Y-modify/YamaX-3.0/Designs/AXBoard/AX-03r/Models/pcb.png

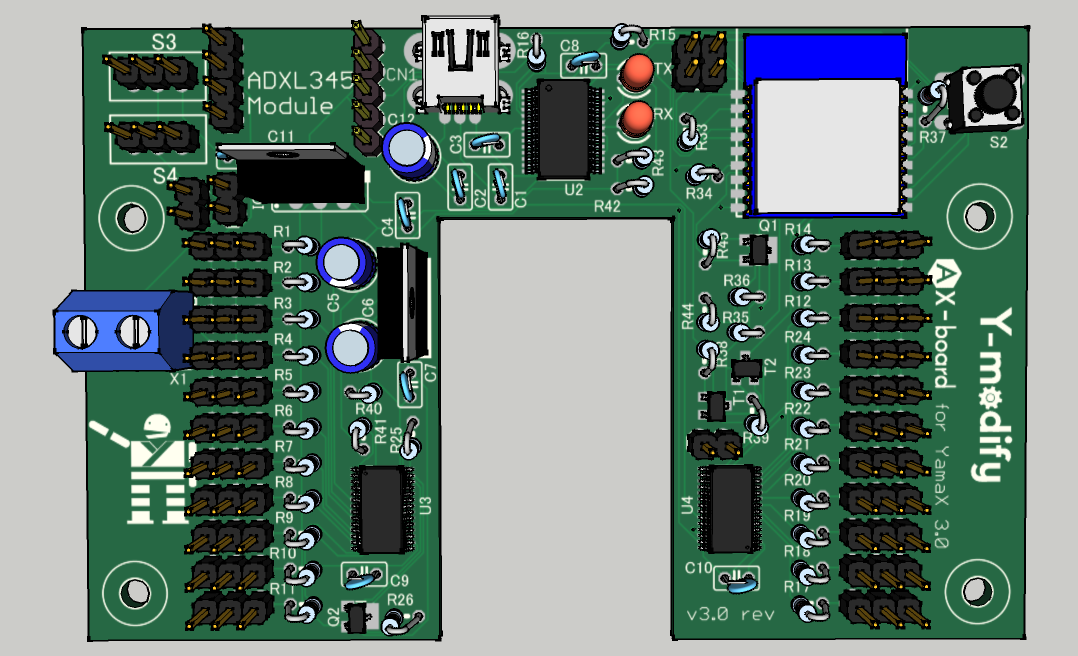
Designs/AXBoard/AX-03r/Models/pcb.png
