Y-modify/YamaX-3.0/Designs/AXBoard/AX-03r/Models/pcb/eagleUp_AX-03r_top_board.png

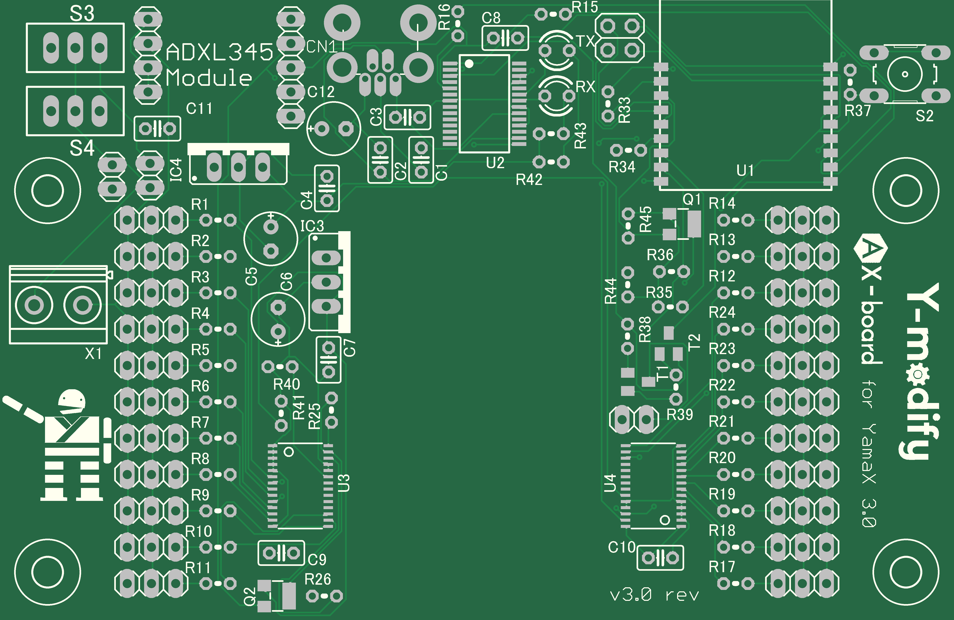
Designs/AXBoard/AX-03r/Models/pcb/eagleUp_AX-03r_top_board.png
