Y-modify/YamaX-3.0/Designs/AXBoard/AX-03r/Previews/Board.png

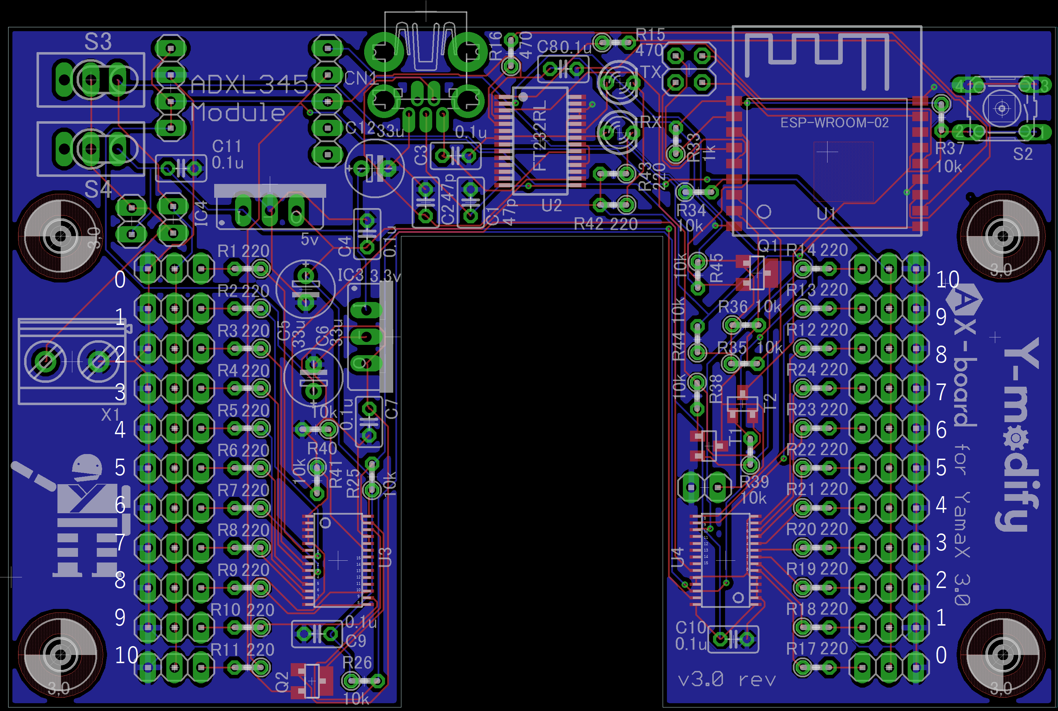
Designs/AXBoard/AX-03r/Previews/Board.png
