Y-modify/YamaX-3.0/Designs/AXBoard/AX-03r/Previews/Front.png

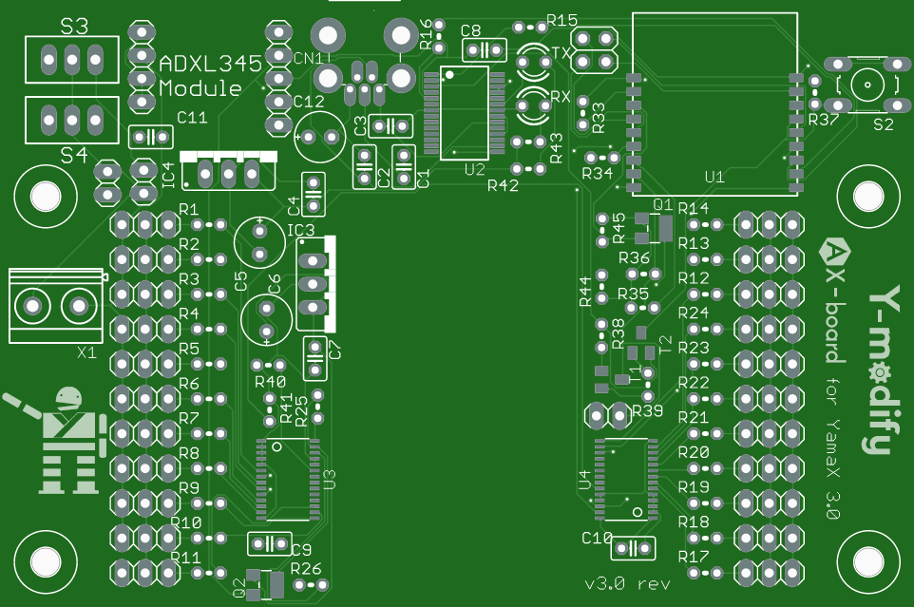
Designs/AXBoard/AX-03r/Previews/Front.png
