Y-modify/YamaX-3.0/Designs/Model/picts/YamaX3.0_redesigned_上.png

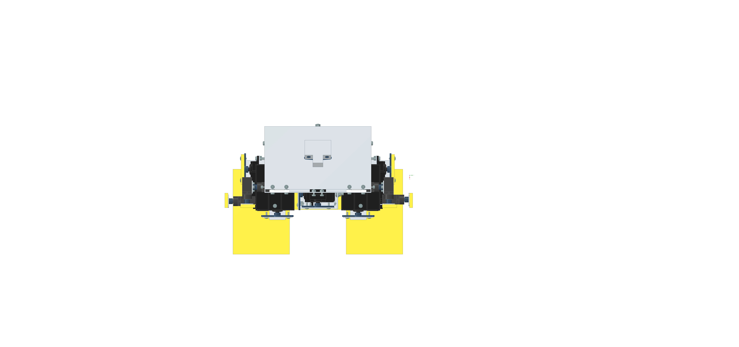
Designs/Model/picts/YamaX3.0_redesigned_上.png
