Y-modify/YamaX-3.0/Designs/Model/picts/YamaX3.0_redesigned_左後ろ.png

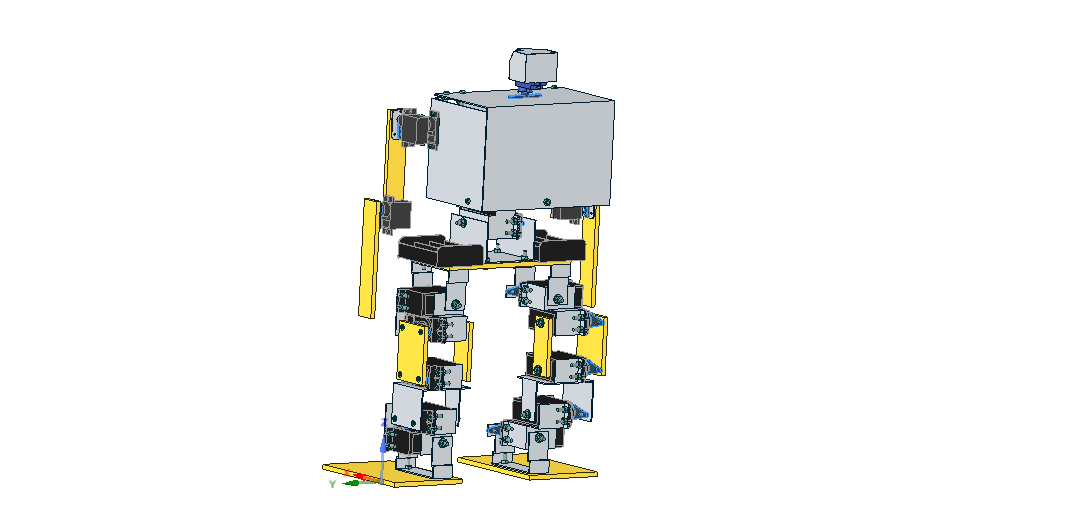
Designs/Model/picts/YamaX3.0_redesigned_左後ろ.png
